seblovett/compassbox/Photos/IMG_20170714_074428.jpg

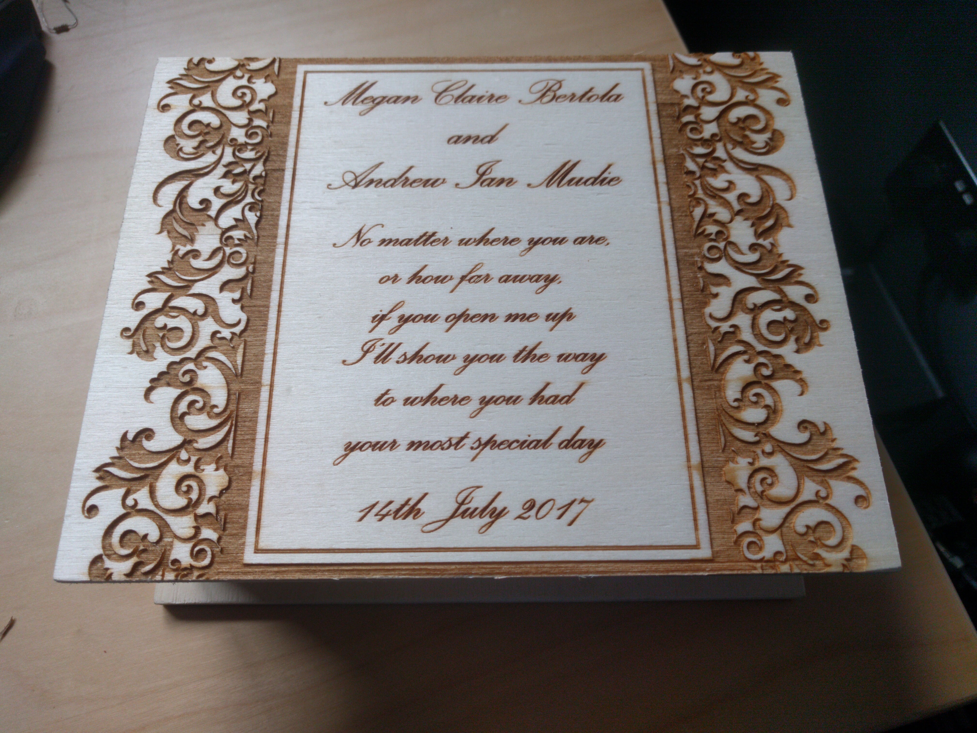
Photos/IMG_20170714_074428.jpg
